cho45/AntennaAnalyzer/software/cordova/www/bower_components/paper-card/demo/cafe.png

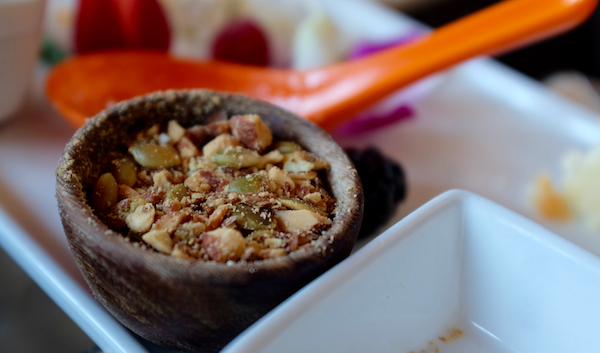
software/cordova/www/bower_components/paper-card/demo/cafe.png
