cho45/AntennaAnalyzer/software/cordova/www/bower_components/paper-card/demo/trip.png

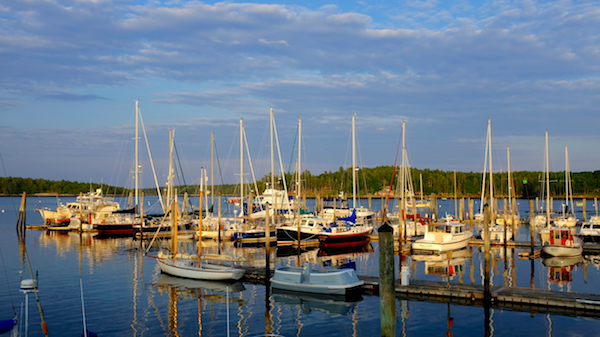
software/cordova/www/bower_components/paper-card/demo/trip.png
