cho45/AntennaAnalyzer/software/cordova/www/bower_components/iron-image/demo/loading.png

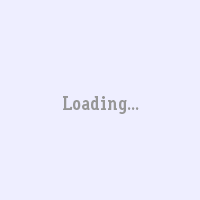
software/cordova/www/bower_components/iron-image/demo/loading.png
